Nobutarou/NiMH_Charger_DIY/v6.0/e2studio/NiMHCharger6.0/src/smc_gen/r_bsp/mcu/rl78_g24/register_access/llvm/iodefine.h

/*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
* Copyright (C) 2023 Renesas Electronics Corporation. All rights reserved.
***********************************************************************************************************************/
/***********************************************************************************************************************
* File Name    : iodefine.h
* Description  : 
***********************************************************************************************************************/
/***********************************************************************************************************************
* History : DD.MM.YYYY Version  Description
*         : 28.02.2023 1.60     First Release.
*         : 30.11.2023 1.62     Updated device file..
***********************************************************************************************************************/

#ifndef __INTRINSIC_FUNCTIONS
#define __INTRINSIC_FUNCTIONS

#define DI() __builtin_rl78_di()
#define EI() __builtin_rl78_ei()
#define HALT() __halt()
#define NOP() __nop()
#define STOP() __stop()

#endif

#ifndef __IOREG_BIT_STRUCTURES
#define __IOREG_BIT_STRUCTURES
typedef struct {
	unsigned char no0 :1;
	unsigned char no1 :1;
	unsigned char no2 :1;
	unsigned char no3 :1;
	unsigned char no4 :1;
	unsigned char no5 :1;
	unsigned char no6 :1;
	unsigned char no7 :1;
} __BITS8;

typedef struct {
	unsigned short no0 :1;
	unsigned short no1 :1;
	unsigned short no2 :1;
	unsigned short no3 :1;
	unsigned short no4 :1;
	unsigned short no5 :1;
	unsigned short no6 :1;
	unsigned short no7 :1;
	unsigned short no8 :1;
	unsigned short no9 :1;
	unsigned short no10 :1;
	unsigned short no11 :1;
	unsigned short no12 :1;
	unsigned short no13 :1;
	unsigned short no14 :1;
	unsigned short no15 :1;
} __BITS16;

#endif

#ifndef IODEFINE_H
#define IODEFINE_H

/*
 IO Registers
 */
union un_p0 {
	unsigned char p0;
	__BITS8 BIT;
};
union un_p1 {
	unsigned char p1;
	__BITS8 BIT;
};
union un_p2 {
	unsigned char p2;
	__BITS8 BIT;
};
union un_p3 {
	unsigned char p3;
	__BITS8 BIT;
};
union un_p4 {
	unsigned char p4;
	__BITS8 BIT;
};
union un_p5 {
	unsigned char p5;
	__BITS8 BIT;
};
union un_p6 {
	unsigned char p6;
	__BITS8 BIT;
};
union un_p7 {
	unsigned char p7;
	__BITS8 BIT;
};
union un_p12 {
	unsigned char p12;
	__BITS8 BIT;
};
union un_p13 {
	unsigned char p13;
	__BITS8 BIT;
};
union un_p14 {
	unsigned char p14;
	__BITS8 BIT;
};
union un_pm0 {
	unsigned char pm0;
	__BITS8 BIT;
};
union un_pm1 {
	unsigned char pm1;
	__BITS8 BIT;
};
union un_pm2 {
	unsigned char pm2;
	__BITS8 BIT;
};
union un_pm3 {
	unsigned char pm3;
	__BITS8 BIT;
};
union un_pm4 {
	unsigned char pm4;
	__BITS8 BIT;
};
union un_pm5 {
	unsigned char pm5;
	__BITS8 BIT;
};
union un_pm6 {
	unsigned char pm6;
	__BITS8 BIT;
};
union un_pm7 {
	unsigned char pm7;
	__BITS8 BIT;
};
union un_pm12 {
	unsigned char pm12;
	__BITS8 BIT;
};
union un_pm14 {
	unsigned char pm14;
	__BITS8 BIT;
};
union un_adm0 {
	unsigned char adm0;
	__BITS8 BIT;
};
union un_ads {
	unsigned char ads;
	__BITS8 BIT;
};
union un_adm1 {
	unsigned char adm1;
	__BITS8 BIT;
};
union un_krctl {
	unsigned char krctl;
	__BITS8 BIT;
};
union un_krm0 {
	unsigned char krm0;
	__BITS8 BIT;
};
union un_egp0 {
	unsigned char egp0;
	__BITS8 BIT;
};
union un_egn0 {
	unsigned char egn0;
	__BITS8 BIT;
};
union un_egp1 {
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
	__BITS8 BIT;
};
union un_pr10h {
	unsigned char pr10h;
	__BITS8 BIT;
};
union un_pr11 {
	unsigned short pr11;
	__BITS16 BIT;
};
union un_pr11l {
	unsigned char pr11l;
	__BITS8 BIT;
};
union un_pr11h {
	unsigned char pr11h;
	__BITS8 BIT;
};
union un_pmc {
	unsigned char pmc;
	__BITS8 BIT;
};

#define P0 (*(volatile union un_p0 *)0xFFF00).p0
#define P0_bit (*(volatile union un_p0 *)0xFFF00).BIT
#define P1 (*(volatile union un_p1 *)0xFFF01).p1
#define P1_bit (*(volatile union un_p1 *)0xFFF01).BIT
#define P2 (*(volatile union un_p2 *)0xFFF02).p2
#define P2_bit (*(volatile union un_p2 *)0xFFF02).BIT
#define P3 (*(volatile union un_p3 *)0xFFF03).p3
#define P3_bit (*(volatile union un_p3 *)0xFFF03).BIT
#define P4 (*(volatile union un_p4 *)0xFFF04).p4
#define P4_bit (*(volatile union un_p4 *)0xFFF04).BIT
#define P5 (*(volatile union un_p5 *)0xFFF05).p5
#define P5_bit (*(volatile union un_p5 *)0xFFF05).BIT
#define P6 (*(volatile union un_p6 *)0xFFF06).p6
#define P6_bit (*(volatile union un_p6 *)0xFFF06).BIT
#define P7 (*(volatile union un_p7 *)0xFFF07).p7
#define P7_bit (*(volatile union un_p7 *)0xFFF07).BIT
#define P12 (*(volatile union un_p12 *)0xFFF0C).p12
#define P12_bit (*(volatile union un_p12 *)0xFFF0C).BIT
#define P13 (*(volatile union un_p13 *)0xFFF0D).p13
#define P13_bit (*(volatile union un_p13 *)0xFFF0D).BIT
#define P14 (*(volatile union un_p14 *)0xFFF0E).p14
#define P14_bit (*(volatile union un_p14 *)0xFFF0E).BIT
#define SDR00 (*(volatile unsigned short *)0xFFF10)
#define TXD0 (*(volatile unsigned char *)0xFFF10)
#define SIO00 (*(volatile unsigned char *)0xFFF10)
#define SDR01 (*(volatile unsigned short *)0xFFF12)
#define RXD0 (*(volatile unsigned char *)0xFFF12)
#define SIO01 (*(volatile unsigned char *)0xFFF12)
#define TDR00 (*(volatile unsigned short *)0xFFF18)
#define TDR01 (*(volatile unsigned short *)0xFFF1A)
#define TDR01L (*(volatile unsigned char *)0xFFF1A)
#define TDR01H (*(volatile unsigned char *)0xFFF1B)
#define ADCR (*(volatile unsigned short *)0xFFF1E)
#define ADCRH (*(volatile unsigned char *)0xFFF1F)
#define PM0 (*(volatile union un_pm0 *)0xFFF20).pm0
#define PM0_bit (*(volatile union un_pm0 *)0xFFF20).BIT
#define PM1 (*(volatile union un_pm1 *)0xFFF21).pm1
#define PM1_bit (*(volatile union un_pm1 *)0xFFF21).BIT
#define PM2 (*(volatile union un_pm2 *)0xFFF22).pm2
#define PM2_bit (*(volatile union un_pm2 *)0xFFF22).BIT
#define PM3 (*(volatile union un_pm3 *)0xFFF23).pm3
#define PM3_bit (*(volatile union un_pm3 *)0xFFF23).BIT
#define PM4 (*(volatile union un_pm4 *)0xFFF24).pm4
#define PM4_bit (*(volatile union un_pm4 *)0xFFF24).BIT
#define PM5 (*(volatile union un_pm5 *)0xFFF25).pm5
#define PM5_bit (*(volatile union un_pm5 *)0xFFF25).BIT
#define PM6 (*(volatile union un_pm6 *)0xFFF26).pm6
#define PM6_bit (*(volatile union un_pm6 *)0xFFF26).BIT
#define PM7 (*(volatile union un_pm7 *)0xFFF27).pm7
#define PM7_bit (*(volatile union un_pm7 *)0xFFF27).BIT
#define PM12 (*(volatile union un_pm12 *)0xFFF2C).pm12
#define PM12_bit (*(volatile union un_pm12 *)0xFFF2C).BIT
#define PM14 (*(volatile union un_pm14 *)0xFFF2E).pm14
#define PM14_bit (*(volatile union un_pm14 *)0xFFF2E).BIT
#define ADM0 (*(volatile union un_adm0 *)0xFFF30).adm0
#define ADM0_bit (*(volatile union un_adm0 *)0xFFF30).BIT
#define ADS (*(volatile union un_ads *)0xFFF31).ads
#define ADS_bit (*(volatile union un_ads *)0xFFF31).BIT
#define ADM1 (*(volatile union un_adm1 *)0xFFF32).adm1
#define ADM1_bit (*(volatile union un_adm1 *)0xFFF32).BIT
#define KRCTL (*(volatile union un_krctl *)0xFFF34).krctl
#define KRCTL_bit (*(volatile union un_krctl *)0xFFF34).BIT
#define KRF (*(volatile unsigned char *)0xFFF35)
#define KRM0 (*(volatile union un_krm0 *)0xFFF37).krm0
#define KRM0_bit (*(volatile union un_krm0 *)0xFFF37).BIT
#define EGP0 (*(volatile union un_egp0 *)0xFFF38).egp0
#define EGP0_bit (*(volatile union un_egp0 *)0xFFF38).BIT
#define EGN0 (*(volatile union un_egn0 *)0xFFF39).egn0
#define EGN0_bit (*(volatile union un_egn0 *)0xFFF39).BIT
#define EGP1 (*(volatile union un_egp1 *)0xFFF3A).egp1
#define EGP1_bit (*(volatile union un_egp1 *)0xFFF3A).BIT
#define EGN1 (*(volatile union un_egn1 *)0xFFF3B).egn1
#define EGN1_bit (*(volatile union un_egn1 *)0xFFF3B).BIT
#define SDR02 (*(volatile unsigned short *)0xFFF44)
#define SIO10 (*(volatile unsigned char *)0xFFF44)
#define TXD1 (*(volatile unsigned char *)0xFFF44)
#define SDR03 (*(volatile unsigned short *)0xFFF46)
#define RXD1 (*(volatile unsigned char *)0xFFF46)
#define SIO11 (*(volatile unsigned char *)0xFFF46)
#define SDR10 (*(volatile unsigned short *)0xFFF48)
#define SIO20 (*(volatile unsigned char *)0xFFF48)
#define TXD2 (*(volatile unsigned char *)0xFFF48)
#define SDR11 (*(volatile unsigned short *)0xFFF4A)
#define SIO21 (*(volatile unsigned char *)0xFFF4A)
#define RXD2 (*(volatile unsigned char *)0xFFF4A)
#define IICA0 (*(volatile unsigned char *)0xFFF50)
#define IICS0 (*(volatile union un_iics0 *)0xFFF51).iics0
#define IICS0_bit (*(volatile union un_iics0 *)0xFFF51).BIT
#define IICF0 (*(volatile union un_iicf0 *)0xFFF52).iicf0
#define IICF0_bit (*(volatile union un_iicf0 *)0xFFF52).BIT
#define TRGGRC (*(volatile unsigned short *)0xFFF60)
#define TRGGRD (*(volatile unsigned short *)0xFFF62)
#define TDR02 (*(volatile unsigned short *)0xFFF64)
#define TDR03 (*(volatile unsigned short *)0xFFF66)
#define TDR03L (*(volatile unsigned char *)0xFFF66)
#define TDR03H (*(volatile unsigned char *)0xFFF67)
#define TRDGRC0 (*(volatile unsigned short *)0xFFF6C)
#define TRDGRD0 (*(volatile unsigned short *)0xFFF6E)
#define TRDGRC1 (*(volatile unsigned short *)0xFFF70)
#define TRDGRD1 (*(volatile unsigned short *)0xFFF72)
#define TRDCMPD0 (*(volatile unsigned short *)0xFFF74)
#define TRDCMPC1 (*(volatile unsigned short *)0xFFF76)
#define TRDCMPD1 (*(volatile unsigned short *)0xFFF78)
#define TRDADTB0 (*(volatile unsigned short *)0xFFF7A)
#define TRDCMPF1 (*(volatile unsigned short *)0xFFF7A)
#define TRDADTB1 (*(volatile unsigned short *)0xFFF7C)
#define TRDRDT (*(volatile unsigned short *)0xFFF7E)
#define TRDRDT0 (*(volatile unsigned char *)0xFFF7E)
#define TRDRDT1 (*(volatile unsigned char *)0xFFF7F)
#define CMC (*(volatile unsigned char *)0xFFFA0)
#define CSC (*(volatile union un_csc *)0xFFFA1).csc
#define CSC_bit (*(volatile union un_csc *)0xFFFA1).BIT
#define OSTC (*(volatile union un_ostc *)0xFFFA2).ostc
#define OSTC_bit (*(volatile union un_ostc *)0xFFFA2).BIT
#define OSTS (*(volatile unsigned char *)0xFFFA3)
#define CKC (*(volatile union un_ckc *)0xFFFA4).ckc
#define CKC_bit (*(volatile union un_ckc *)0xFFFA4).BIT
#define CKS0 (*(volatile union un_cks0 *)0xFFFA5).cks0
#define CKS0_bit (*(volatile union un_cks0 *)0xFFFA5).BIT
#define CKS1 (*(volatile union un_cks1 *)0xFFFA6).cks1
#define CKS1_bit (*(volatile union un_cks1 *)0xFFFA6).BIT
#define CKSEL (*(volatile union un_cksel *)0xFFFA7).cksel
#define CKSEL_bit (*(volatile union un_cksel *)0xFFFA7).BIT
#define RESF (*(volatile unsigned char *)0xFFFA8)
#define LVIM (*(volatile union un_lvim *)0xFFFA9).lvim
#define LVIM_bit (*(volatile union un_lvim *)0xFFFA9).BIT
#define LVIS (*(volatile union un_lvis *)0xFFFAA).lvis
#define LVIS_bit (*(volatile union un_lvis *)0xFFFAA).BIT
#define WDTE (*(volatile unsigned char *)0xFFFAB)
#define CRCIN (*(volatile unsigned char *)0xFFFAC)
#define IF2 (*(volatile union un_if2 *)0xFFFD0).if2
#define IF2_bit (*(volatile union un_if2 *)0xFFFD0).BIT
#define IF2L (*(volatile union un_if2l *)0xFFFD0).if2l
#define IF2L_bit (*(volatile union un_if2l *)0xFFFD0).BIT
#define IF2H (*(volatile union un_if2h *)0xFFFD1).if2h
#define IF2H_bit (*(volatile union un_if2h *)0xFFFD1).BIT
#define IF3 (*(volatile union un_if3 *)0xFFFD2).if3
#define IF3_bit (*(volatile union un_if3 *)0xFFFD2).BIT
#define IF3L (*(volatile union un_if3l *)0xFFFD2).if3l
#define IF3L_bit (*(volatile union un_if3l *)0xFFFD2).BIT
#define IF3H (*(volatile union un_if3h *)0xFFFD3).if3h
#define IF3H_bit (*(volatile union un_if3h *)0xFFFD3).BIT
#define MK2 (*(volatile union un_mk2 *)0xFFFD4).mk2
#define MK2_bit (*(volatile union un_mk2 *)0xFFFD4).BIT
#define MK2L (*(volatile union un_mk2l *)0xFFFD4).mk2l
#define MK2L_bit (*(volatile union un_mk2l *)0xFFFD4).BIT
#define MK2H (*(volatile union un_mk2h *)0xFFFD5).mk2h
#define MK2H_bit (*(volatile union un_mk2h *)0xFFFD5).BIT
#define MK3 (*(volatile union un_mk3 *)0xFFFD6).mk3
#define MK3_bit (*(volatile union un_mk3 *)0xFFFD6).BIT
#define MK3L (*(volatile union un_mk3l *)0xFFFD6).mk3l
#define MK3L_bit (*(volatile union un_mk3l *)0xFFFD6).BIT
#define MK3H (*(volatile union un_mk3h *)0xFFFD7).mk3h
#define MK3H_bit (*(volatile union un_mk3h *)0xFFFD7).BIT
#define PR02 (*(volatile union un_pr02 *)0xFFFD8).pr02
#define PR02_bit (*(volatile union un_pr02 *)0xFFFD8).BIT
#define PR02L (*(volatile union un_pr02l *)0xFFFD8).pr02l
#define PR02L_bit (*(volatile union un_pr02l *)0xFFFD8).BIT
#define PR02H (*(volatile union un_pr02h *)0xFFFD9).pr02h
#define PR02H_bit (*(volatile union un_pr02h *)0xFFFD9).BIT
#define PR03 (*(volatile union un_pr03 *)0xFFFDA).pr03
#define PR03_bit (*(volatile union un_pr03 *)0xFFFDA).BIT
#define PR03L (*(volatile union un_pr03l *)0xFFFDA).pr03l
#define PR03L_bit (*(volatile union un_pr03l *)0xFFFDA).BIT
#define PR03H (*(volatile union un_pr03h *)0xFFFDB).pr03h
#define PR03H_bit (*(volatile union un_pr03h *)0xFFFDB).BIT
#define PR12 (*(volatile union un_pr12 *)0xFFFDC).pr12
#define PR12_bit (*(volatile union un_pr12 *)0xFFFDC).BIT
#define PR12L (*(volatile union un_pr12l *)0xFFFDC).pr12l
#define PR12L_bit (*(volatile union un_pr12l *)0xFFFDC).BIT
#define PR12H (*(volatile union un_pr12h *)0xFFFDD).pr12h
#define PR12H_bit (*(volatile union un_pr12h *)0xFFFDD).BIT
#define PR13 (*(volatile union un_pr13 *)0xFFFDE).pr13
#define PR13_bit (*(volatile union un_pr13 *)0xFFFDE).BIT
#define PR13L (*(volatile union un_pr13l *)0xFFFDE).pr13l
#define PR13L_bit (*(volatile union un_pr13l *)0xFFFDE).BIT
#define PR13H (*(volatile union un_pr13h *)0xFFFDF).pr13h
#define PR13H_bit (*(volatile union un_pr13h *)0xFFFDF).BIT
#define IF0 (*(volatile union un_if0 *)0xFFFE0).if0
#define IF0_bit (*(volatile union un_if0 *)0xFFFE0).BIT
#define IF0L (*(volatile union un_if0l *)0xFFFE0).if0l
#define IF0L_bit (*(volatile union un_if0l *)0xFFFE0).BIT
#define IF0H (*(volatile union un_if0h *)0xFFFE1).if0h
#define IF0H_bit (*(volatile union un_if0h *)0xFFFE1).BIT
#define IF1 (*(volatile union un_if1 *)0xFFFE2).if1
#define IF1_bit (*(volatile union un_if1 *)0xFFFE2).BIT
#define IF1L (*(volatile union un_if1l *)0xFFFE2).if1l
#define IF1L_bit (*(volatile union un_if1l *)0xFFFE2).BIT
#define IF1H (*(volatile union un_if1h *)0xFFFE3).if1h
#define IF1H_bit (*(volatile union un_if1h *)0xFFFE3).BIT
#define MK0 (*(volatile union un_mk0 *)0xFFFE4).mk0
#define MK0_bit (*(volatile union un_mk0 *)0xFFFE4).BIT
#define MK0L (*(volatile union un_mk0l *)0xFFFE4).mk0l
#define MK0L_bit (*(volatile union un_mk0l *)0xFFFE4).BIT
#define MK0H (*(volatile union un_mk0h *)0xFFFE5).mk0h
#define MK0H_bit (*(volatile union un_mk0h *)0xFFFE5).BIT
#define MK1 (*(volatile union un_mk1 *)0xFFFE6).mk1
#define MK1_bit (*(volatile union un_mk1 *)0xFFFE6).BIT
#define MK1L (*(volatile union un_mk1l *)0xFFFE6).mk1l
#define MK1L_bit (*(volatile union un_mk1l *)0xFFFE6).BIT
#define MK1H (*(volatile union un_mk1h *)0xFFFE7).mk1h
#define MK1H_bit (*(volatile union un_mk1h *)0xFFFE7).BIT
#define PR00 (*(volatile union un_pr00 *)0xFFFE8).pr00
#define PR00_bit (*(volatile union un_pr00 *)0xFFFE8).BIT
#define PR00L (*(volatile union un_pr00l *)0xFFFE8).pr00l
#define PR00L_bit (*(volatile union un_pr00l *)0xFFFE8).BIT
#define PR00H (*(volatile union un_pr00h *)0xFFFE9).pr00h
#define PR00H_bit (*(volatile union un_pr00h *)0xFFFE9).BIT
#define PR01 (*(volatile union un_pr01 *)0xFFFEA).pr01
#define PR01_bit (*(volatile union un_pr01 *)0xFFFEA).BIT
#define PR01L (*(volatile union un_pr01l *)0xFFFEA).pr01l
#define PR01L_bit (*(volatile union un_pr01l *)0xFFFEA).BIT
#define PR01H (*(volatile union un_pr01h *)0xFFFEB).pr01h
#define PR01H_bit (*(volatile union un_pr01h *)0xFFFEB).BIT
#define PR10 (*(volatile union un_pr10 *)0xFFFEC).pr10
#define PR10_bit (*(volatile union un_pr10 *)0xFFFEC).BIT
#define PR10L (*(volatile union un_pr10l *)0xFFFEC).pr10l
#define PR10L_bit (*(volatile union un_pr10l *)0xFFFEC).BIT
#define PR10H (*(volatile union un_pr10h *)0xFFFED).pr10h
#define PR10H_bit (*(volatile union un_pr10h *)0xFFFED).BIT
#define PR11 (*(volatile union un_pr11 *)0xFFFEE).pr11
#define PR11_bit (*(volatile union un_pr11 *)0xFFFEE).BIT
#define PR11L (*(volatile union un_pr11l *)0xFFFEE).pr11l
#define PR11L_bit (*(volatile union un_pr11l *)0xFFFEE).BIT
#define PR11H (*(volatile union un_pr11h *)0xFFFEF).pr11h
#define PR11H_bit (*(volatile union un_pr11h *)0xFFFEF).BIT
#define MACRL (*(volatile unsigned short *)0xFFFF0)
#define MACRH (*(volatile unsigned short *)0xFFFF2)
#define PMC (*(volatile union un_pmc *)0xFFFFE).pmc
#define PMC_bit (*(volatile union un_pmc *)0xFFFFE).BIT

/*
 Sfr bits
 */
#define ADCE ADM0_bit.no0
#define ADCS ADM0_bit.no7
#define KREG KRCTL_bit.no0
#define KRMD KRCTL_bit.no7
#define SPD0 IICS0_bit.no0
#define STD0 IICS0_bit.no1
#define ACKD0 IICS0_bit.no2
#define TRC0 IICS0_bit.no3
#define COI0 IICS0_bit.no4
#define EXC0 IICS0_bit.no5
#define ALD0 IICS0_bit.no6
#define MSTS0 IICS0_bit.no7
#define IICRSV0 IICF0_bit.no0
#define STCEN0 IICF0_bit.no1
#define IICBSY0 IICF0_bit.no6
#define STCF0 IICF0_bit.no7
#define HIOSTOP CSC_bit.no0
#define MIOEN CSC_bit.no1
#define XTSTOP CSC_bit.no6
#define MSTOP CSC_bit.no7
#define MCM1 CKC_bit.no0
#define MCS1 CKC_bit.no1
#define MCM0 CKC_bit.no4
#define MCS CKC_bit.no5
#define CSS CKC_bit.no6
#define CLS CKC_bit.no7
#define PCLOE0 CKS0_bit.no7
#define PCLOE1 CKS1_bit.no7
#define SELLOSC CKSEL_bit.no0
#define LVD0F LVIM_bit.no0
#define LVD1F LVIM_bit.no1
#define DLVD0F LVIM_bit.no2
#define DLVD1F LVIM_bit.no3
#define LVISEN LVIM_bit.no7
#define LVD1SEL LVIS_bit.no6
#define LVD1EN LVIS_bit.no7
#define BPDIF IF2L_bit.no0
#define CLDIF IF2L_bit.no0
#define TRXIF IF2L_bit.no0
#define EDIF IF2L_bit.no0
#define PIF20 IF2L_bit.no1
#define PIF21 IF2L_bit.no2
#define PIF6 IF2L_bit.no3
#define TMKBSTRIF10 IF2L_bit.no3
#define PIF7 IF2L_bit.no4
#define TMKBSTPIF10 IF2L_bit.no4
#define TMKBSTRIF11 IF2L_bit.no5
#define PIF8 IF2L_bit.no5
#define PIF9 IF2L_bit.no6
#define TMKBSTPIF11 IF2L_bit.no6
#define FLIF IF2L_bit.no7
#define PIF10 IF2H_bit.no0
#define CMPIF0 IF2H_bit.no0
#define PIF11 IF2H_bit.no1
#define CMPIF1 IF2H_bit.no1
#define FAATRAPIF IF2H_bit.no2
#define CMPIF2 IF2H_bit.no3
#define CMPIF3 IF2H_bit.no4
#define TMKBIF0 IF2H_bit.no5
#define TMKBIF1 IF2H_bit.no6
#define TMKBIF2 IF2H_bit.no7
#define SDDIF IF3L_bit.no0
#define GCRIF IF3L_bit.no0
#define PMCIF IF3L_bit.no1
#define FEDIF IF3L_bit.no1
#define TMKBSTRIF00 IF3L_bit.no2
#define TMKBSTPIF00 IF3L_bit.no3
#define TMKBSTRIF01 IF3L_bit.no4
#define TMKBSTPIF01 IF3L_bit.no5
#define TMKBSTRIF20 IF3L_bit.no6
#define TMKBSTPIF20 IF3L_bit.no7
#define TMKBSTRIF21 IF3H_bit.no0
#define TMKBSTPIF21 IF3H_bit.no1
#define TIMECIF1 IF3H_bit.no2
#define TIMECIF2 IF3H_bit.no3
#define ADIF3 IF3H_bit.no4
#define EDMK MK2L_bit.no0
#define TRXMK MK2L_bit.no0
#define BPDMK MK2L_bit.no0
#define CLDMK MK2L_bit.no0
#define PMK20 MK2L_bit.no1
#define PMK21 MK2L_bit.no2
#define PMK6 MK2L_bit.no3
#define TMKBSTRMK10 MK2L_bit.no3
#define PMK7 MK2L_bit.no4
#define TMKBSTPMK10 MK2L_bit.no4
#define PMK8 MK2L_bit.no5
#define TMKBSTRMK11 MK2L_bit.no5
#define TMKBSTPMK11 MK2L_bit.no6
#define PMK9 MK2L_bit.no6
#define FLMK MK2L_bit.no7
#define PMK10 MK2H_bit.no0
#define CMPMK0 MK2H_bit.no0
#define PMK11 MK2H_bit.no1
#define CMPMK1 MK2H_bit.no1
#define FAATRAPMK MK2H_bit.no2
#define CMPMK2 MK2H_bit.no3
#define CMPMK3 MK2H_bit.no4
#define TMKBMK0 MK2H_bit.no5
#define TMKBMK1 MK2H_bit.no6
#define TMKBMK2 MK2H_bit.no7
#define GCRMK MK3L_bit.no0
#define SDDMK MK3L_bit.no0
#define PMCMK MK3L_bit.no1
#define FEDMK MK3L_bit.no1
#define TMKBSTRMK00 MK3L_bit.no2
#define TMKBSTPMK00 MK3L_bit.no3
#define TMKBSTRMK01 MK3L_bit.no4
#define TMKBSTPMK01 MK3L_bit.no5
#define TMKBSTRMK20 MK3L_bit.no6
#define TMKBSTPMK20 MK3L_bit.no7
#define TMKBSTRMK21 MK3H_bit.no0
#define TMKBSTPMK21 MK3H_bit.no1
#define TIMECMK1 MK3H_bit.no2
#define TIMECMK2 MK3H_bit.no3
#define ADMK3 MK3H_bit.no4
#define EDPR0 PR02L_bit.no0
#define TRXPR0 PR02L_bit.no0
#define BPDPR0 PR02L_bit.no0
#define CLDPR0 PR02L_bit.no0
#define PPR020 PR02L_bit.no1
#define PPR021 PR02L_bit.no2
#define TMKBSTRPR010 PR02L_bit.no3
#define PPR06 PR02L_bit.no3
#define TMKBSTPPR010 PR02L_bit.no4
#define PPR07 PR02L_bit.no4
#define TMKBSTRPR011 PR02L_bit.no5
#define PPR08 PR02L_bit.no5
#define PPR09 PR02L_bit.no6
#define TMKBSTPPR011 PR02L_bit.no6
#define FLPR0 PR02L_bit.no7
#define PPR010 PR02H_bit.no0
#define CMPPR00 PR02H_bit.no0
#define PPR011 PR02H_bit.no1
#define CMPPR01 PR02H_bit.no1
#define FAATRAPPR0 PR02H_bit.no2
#define CMPPR02 PR02H_bit.no3
#define CMPPR03 PR02H_bit.no4
#define TMKBPR00 PR02H_bit.no5
#define TMKBPR01 PR02H_bit.no6
#define TMKBPR02 PR02H_bit.no7
#define SDDPR0 PR03L_bit.no0
#define GCRPR0 PR03L_bit.no0
#define PMCPR0 PR03L_bit.no1
#define FEDPR0 PR03L_bit.no1
#define TMKBSTRPR000 PR03L_bit.no2
#define TMKBSTPPR000 PR03L_bit.no3
#define TMKBSTRPR001 PR03L_bit.no4
#define TMKBSTPPR001 PR03L_bit.no5
#define TMKBSTRPR020 PR03L_bit.no6
#define TMKBSTPPR020 PR03L_bit.no7
#define TMKBSTRPR021 PR03H_bit.no0
#define TMKBSTPPR021 PR03H_bit.no1
#define TIMECPR01 PR03H_bit.no2
#define TIMECPR02 PR03H_bit.no3
#define ADPR03 PR03H_bit.no4
#define EDPR1 PR12L_bit.no0
#define BPDPR1 PR12L_bit.no0
#define TRXPR1 PR12L_bit.no0
#define CLDPR1 PR12L_bit.no0
#define PPR120 PR12L_bit.no1
#define PPR121 PR12L_bit.no2
#define PPR16 PR12L_bit.no3
#define TMKBSTRPR110 PR12L_bit.no3
#define PPR17 PR12L_bit.no4
#define TMKBSTPPR110 PR12L_bit.no4
#define PPR18 PR12L_bit.no5
#define TMKBSTRPR111 PR12L_bit.no5
#define PPR19 PR12L_bit.no6
#define TMKBSTPPR111 PR12L_bit.no6
#define FLPR1 PR12L_bit.no7
#define PPR110 PR12H_bit.no0
#define CMPPR10 PR12H_bit.no0
#define PPR111 PR12H_bit.no1
#define CMPPR11 PR12H_bit.no1
#define FAATRAPPR1 PR12H_bit.no2
#define CMPPR12 PR12H_bit.no3
#define CMPPR13 PR12H_bit.no4
#define TMKBPR10 PR12H_bit.no5
#define TMKBPR11 PR12H_bit.no6
#define TMKBPR12 PR12H_bit.no7
#define SDDPR1 PR13L_bit.no0
#define GCRPR1 PR13L_bit.no0
#define PMCPR1 PR13L_bit.no1
#define FEDPR1 PR13L_bit.no1
#define TMKBSTRPR100 PR13L_bit.no2
#define TMKBSTPPR100 PR13L_bit.no3
#define TMKBSTRPR101 PR13L_bit.no4
#define TMKBSTPPR101 PR13L_bit.no5
#define TMKBSTRPR120 PR13L_bit.no6
#define TMKBSTPPR120 PR13L_bit.no7
#define TMKBSTRPR121 PR13H_bit.no0
#define TMKBSTPPR121 PR13H_bit.no1
#define TIMECPR11 PR13H_bit.no2
#define TIMECPR12 PR13H_bit.no3
#define ADPR13 PR13H_bit.no4
#define WDTIIF IF0L_bit.no0
#define LVIIF IF0L_bit.no1
#define PIF0 IF0L_bit.no2
#define PIF1 IF0L_bit.no3
#define ADIF1 IF0L_bit.no3
#define PIF2 IF0L_bit.no4
#define ADIF2 IF0L_bit.no4
#define PIF3 IF0L_bit.no5
#define PIF4 IF0L_bit.no6
#define PIF5 IF0L_bit.no7
#define STIF2 IF0H_bit.no0
#define CSIIF20 IF0H_bit.no0
#define IICIF20 IF0H_bit.no0
#define SRIF2 IF0H_bit.no1
#define IICIF21 IF0H_bit.no1
#define CSIIF21 IF0H_bit.no1
#define SREIF2 IF0H_bit.no2
#define FAAEIF IF0H_bit.no3
#define TIMECIF0 IF0H_bit.no4
#define STIF0 IF0H_bit.no5
#define IICIF00 IF0H_bit.no5
#define CSIIF00 IF0H_bit.no5
#define TMIF00 IF0H_bit.no6
#define SREIF0 IF0H_bit.no7
#define TMIF01H IF0H_bit.no7
#define STIF1 IF1L_bit.no0
#define IICIF10 IF1L_bit.no0
#define CSIIF10 IF1L_bit.no0
#define SRIF1 IF1L_bit.no1
#define CSIIF11 IF1L_bit.no1
#define IICIF11 IF1L_bit.no1
#define SREIF1 IF1L_bit.no2
#define TMIF03H IF1L_bit.no2
#define IICAIF0 IF1L_bit.no3
#define SRIF0 IF1L_bit.no4
#define CSIIF01 IF1L_bit.no4
#define IICIF01 IF1L_bit.no4
#define TMIF01 IF1L_bit.no5
#define TMIF02 IF1L_bit.no6
#define TMIF03 IF1L_bit.no7
#define ADIF0 IF1H_bit.no0
#define RTCIF IF1H_bit.no1
#define ITLIF IF1H_bit.no2
#define KRIF IF1H_bit.no3
#define TDIF IF1H_bit.no4
#define TRJIF0 IF1H_bit.no4
#define TRDIF0 IF1H_bit.no5
#define TRDIF1 IF1H_bit.no6
#define TRGIF IF1H_bit.no7
#define RDIF IF1H_bit.no7
#define WDTIMK MK0L_bit.no0
#define LVIMK MK0L_bit.no1
#define PMK0 MK0L_bit.no2
#define PMK1 MK0L_bit.no3
#define ADMK1 MK0L_bit.no3
#define ADMK2 MK0L_bit.no4
#define PMK2 MK0L_bit.no4
#define PMK3 MK0L_bit.no5
#define PMK4 MK0L_bit.no6
#define PMK5 MK0L_bit.no7
#define IICMK20 MK0H_bit.no0
#define CSIMK20 MK0H_bit.no0
#define STMK2 MK0H_bit.no0
#define SRMK2 MK0H_bit.no1
#define CSIMK21 MK0H_bit.no1
#define IICMK21 MK0H_bit.no1
#define SREMK2 MK0H_bit.no2
#define FAAEMK MK0H_bit.no3
#define TIMECMK0 MK0H_bit.no4
#define IICMK00 MK0H_bit.no5
#define CSIMK00 MK0H_bit.no5
#define STMK0 MK0H_bit.no5
#define TMMK00 MK0H_bit.no6
#define SREMK0 MK0H_bit.no7
#define TMMK01H MK0H_bit.no7
#define STMK1 MK1L_bit.no0
#define CSIMK10 MK1L_bit.no0
#define IICMK10 MK1L_bit.no0
#define SRMK1 MK1L_bit.no1
#define IICMK11 MK1L_bit.no1
#define CSIMK11 MK1L_bit.no1
#define SREMK1 MK1L_bit.no2
#define TMMK03H MK1L_bit.no2
#define IICAMK0 MK1L_bit.no3
#define SRMK0 MK1L_bit.no4
#define IICMK01 MK1L_bit.no4
#define CSIMK01 MK1L_bit.no4
#define TMMK01 MK1L_bit.no5
#define TMMK02 MK1L_bit.no6
#define TMMK03 MK1L_bit.no7
#define ADMK0 MK1H_bit.no0
#define RTCMK MK1H_bit.no1
#define ITLMK MK1H_bit.no2
#define KRMK MK1H_bit.no3
#define TDMK MK1H_bit.no4
#define TRJMK0 MK1H_bit.no4
#define TRDMK0 MK1H_bit.no5
#define TRDMK1 MK1H_bit.no6
#define TRGMK MK1H_bit.no7
#define RDMK MK1H_bit.no7
#define WDTIPR0 PR00L_bit.no0
#define LVIPR0 PR00L_bit.no1
#define PPR00 PR00L_bit.no2
#define PPR01 PR00L_bit.no3
#define ADPR01 PR00L_bit.no3
#define PPR02 PR00L_bit.no4
#define ADPR02 PR00L_bit.no4
#define PPR03 PR00L_bit.no5
#define PPR04 PR00L_bit.no6
#define PPR05 PR00L_bit.no7
#define CSIPR020 PR00H_bit.no0
#define IICPR020 PR00H_bit.no0
#define STPR02 PR00H_bit.no0
#define SRPR02 PR00H_bit.no1
#define CSIPR021 PR00H_bit.no1
#define IICPR021 PR00H_bit.no1
#define SREPR02 PR00H_bit.no2
#define FAAEPR0 PR00H_bit.no3
#define TIMECPR00 PR00H_bit.no4
#define CSIPR000 PR00H_bit.no5
#define IICPR000 PR00H_bit.no5
#define STPR00 PR00H_bit.no5
#define TMPR000 PR00H_bit.no6
#define SREPR00 PR00H_bit.no7
#define TMPR001H PR00H_bit.no7
#define CSIPR010 PR01L_bit.no0
#define IICPR010 PR01L_bit.no0
#define STPR01 PR01L_bit.no0
#define SRPR01 PR01L_bit.no1
#define CSIPR011 PR01L_bit.no1
#define IICPR011 PR01L_bit.no1
#define SREPR01 PR01L_bit.no2
#define TMPR003H PR01L_bit.no2
#define IICAPR00 PR01L_bit.no3
#define SRPR00 PR01L_bit.no4
#define CSIPR001 PR01L_bit.no4
#define IICPR001 PR01L_bit.no4
#define TMPR001 PR01L_bit.no5
#define TMPR002 PR01L_bit.no6
#define TMPR003 PR01L_bit.no7
#define ADPR00 PR01H_bit.no0
#define RTCPR0 PR01H_bit.no1
#define ITLPR0 PR01H_bit.no2
#define KRPR0 PR01H_bit.no3
#define TRJPR00 PR01H_bit.no4
#define TDPR0 PR01H_bit.no4
#define TRDPR00 PR01H_bit.no5
#define TRDPR01 PR01H_bit.no6
#define TRGPR0 PR01H_bit.no7
#define RDPR0 PR01H_bit.no7
#define WDTIPR1 PR10L_bit.no0
#define LVIPR1 PR10L_bit.no1
#define PPR10 PR10L_bit.no2
#define PPR11 PR10L_bit.no3
#define ADPR11 PR10L_bit.no3
#define PPR12 PR10L_bit.no4
#define ADPR12 PR10L_bit.no4
#define PPR13 PR10L_bit.no5
#define PPR14 PR10L_bit.no6
#define PPR15 PR10L_bit.no7
#define IICPR120 PR10H_bit.no0
#define CSIPR120 PR10H_bit.no0
#define STPR12 PR10H_bit.no0
#define IICPR121 PR10H_bit.no1
#define CSIPR121 PR10H_bit.no1
#define SRPR12 PR10H_bit.no1
#define SREPR12 PR10H_bit.no2
#define FAAEPR1 PR10H_bit.no3
#define TIMECPR10 PR10H_bit.no4
#define CSIPR100 PR10H_bit.no5
#define IICPR100 PR10H_bit.no5
#define STPR10 PR10H_bit.no5
#define TMPR100 PR10H_bit.no6
#define TMPR101H PR10H_bit.no7
#define SREPR10 PR10H_bit.no7
#define IICPR110 PR11L_bit.no0
#define STPR11 PR11L_bit.no0
#define CSIPR110 PR11L_bit.no0
#define IICPR111 PR11L_bit.no1
#define CSIPR111 PR11L_bit.no1
#define SRPR11 PR11L_bit.no1
#define SREPR11 PR11L_bit.no2
#define TMPR103H PR11L_bit.no2
#define IICAPR10 PR11L_bit.no3
#define IICPR101 PR11L_bit.no4
#define SRPR10 PR11L_bit.no4
#define CSIPR101 PR11L_bit.no4
#define TMPR101 PR11L_bit.no5
#define TMPR102 PR11L_bit.no6
#define TMPR103 PR11L_bit.no7
#define ADPR10 PR11H_bit.no0
#define RTCPR1 PR11H_bit.no1
#define ITLPR1 PR11H_bit.no2
#define KRPR1 PR11H_bit.no3
#define TDPR1 PR11H_bit.no4
#define TRJPR10 PR11H_bit.no4
#define TRDPR10 PR11H_bit.no5
#define TRDPR11 PR11H_bit.no6
#define TRGPR1 PR11H_bit.no7
#define RDPR1 PR11H_bit.no7
#define MAA PMC_bit.no0

/*
 Interrupt vector addresses
 */
#define RST_vect 0x0
#define INTDBG_vect 0x2
#define INTWDTI_vect 0x4
#define INTLVI_vect 0x6
#define INTP0_vect 0x8
#define INTAD1_vect 0xA
#define INTP1_vect 0xA
#define INTAD2_vect 0xC
#define INTP2_vect 0xC
#define INTP3_vect 0xE
#define INTP4_vect 0x10
#define INTP5_vect 0x12
#define INTCSI20_vect 0x14
#define INTIIC20_vect 0x14
#define INTST2_vect 0x14
#define INTCSI21_vect 0x16
#define INTIIC21_vect 0x16
#define INTSR2_vect 0x16
#define INTSRE2_vect 0x18
#define INTFAAE_vect 0x1A
#define INTTIMEC0_vect 0x1C
#define INTCSI00_vect 0x1E
#define INTIIC00_vect 0x1E
#define INTST0_vect 0x1E
#define INTTM00_vect 0x20
#define INTSRE0_vect 0x22
#define INTTM01H_vect 0x22
#define INTCSI10_vect 0x24
#define INTIIC10_vect 0x24
#define INTST1_vect 0x24
#define INTCSI11_vect 0x26
#define INTIIC11_vect 0x26
#define INTSR1_vect 0x26
#define INTSRE1_vect 0x28
#define INTTM03H_vect 0x28
#define INTIICA0_vect 0x2A
#define INTCSI01_vect 0x2C
#define INTIIC01_vect 0x2C
#define INTSR0_vect 0x2C
#define INTTM01_vect 0x2E
#define INTTM02_vect 0x30
#define INTTM03_vect 0x32
#define INTAD0_vect 0x34
#define INTRTC_vect 0x36
#define INTITL_vect 0x38
#define INTKR_vect 0x3A
#define INTTD_vect 0x3C
#define INTTRJ0_vect 0x3C
#define INTTRD0_vect 0x3E
#define INTTRD1_vect 0x40
#define INTRD_vect 0x42
#define INTTRG_vect 0x42
#define INTBPD_vect 0x44
#define INTCLD_vect 0x44
#define INTED_vect 0x44
#define INTTRX_vect 0x44
#define INTP20_vect 0x46
#define INTP21_vect 0x48
#define INTP6_vect 0x4A
#define INTTMKBSTR10_vect 0x4A
#define INTP7_vect 0x4C
#define INTTMKBSTP10_vect 0x4C
#define INTP8_vect 0x4E
#define INTTMKBSTR11_vect 0x4E
#define INTP9_vect 0x50
#define INTTMKBSTP11_vect 0x50
#define INTFL_vect 0x52
#define INTCMP0_vect 0x54
#define INTP10_vect 0x54
#define INTCMP1_vect 0x56
#define INTP11_vect 0x56
#define INTFAATRAP_vect 0x58
#define INTCMP2_vect 0x5A
#define INTCMP3_vect 0x5C
#define INTTMKB0_vect 0x5E
#define INTTMKB1_vect 0x60
#define INTTMKB2_vect 0x62
#define INTGCR_vect 0x64
#define INTSDD_vect 0x64
#define INTFED_vect 0x66
#define INTPMC_vect 0x66
#define INTTMKBSTR00_vect 0x68
#define INTTMKBSTP00_vect 0x6A
#define INTTMKBSTR01_vect 0x6C
#define INTTMKBSTP01_vect 0x6E
#define INTTMKBSTR20_vect 0x70
#define INTTMKBSTP20_vect 0x72
#define INTTMKBSTR21_vect 0x74
#define INTTMKBSTP21_vect 0x76
#define INTTIMEC1_vect 0x78
#define INTTIMEC2_vect 0x7A
#define INTAD3_vect 0x7C
#define BRK_I_vect 0x7E
#endif
