Nobutarou/NiMH_Charger_DIY/v6.0/e2studio/NiMHCharger6.0/src/smc_gen/general/r_cg_inthandler.c

/*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
* Copyright (C) 2021, 2025 Renesas Electronics Corporation. All rights reserved.
***********************************************************************************************************************/

/***********************************************************************************************************************
* File Name        : r_cg_inthandler.c
* Version          : 1.0.50
* Device(s)        : R7F101G6ExSP
* Description      : None
***********************************************************************************************************************/

/***********************************************************************************************************************
Includes
***********************************************************************************************************************/
#include "r_cg_interrupt_handlers.h"

/*
 * INT_WDTI (0x4)
 */
void INT_WDTI (void)
{
    /* Start user code for INT_WDTI. Do not edit comment generated here */
    /* End user code. Do not edit comment generated here */
}

/*
 * INT_LVI (0x6)
 */
void INT_LVI (void)
{
    /* Start user code for INT_LVI. Do not edit comment generated here */
    /* End user code. Do not edit comment generated here */
}

/*
 * INT_P0 (0x8)
 */
void INT_P0 (void)
{
    /* Start user code for INT_P0. Do not edit comment generated here */
    /* End user code. Do not edit comment generated here */
}

/*
 * INT_P1/INT_AD1 (0xA)
 */
void INT_P1 (void)
{
    /* Start user code for INT_P1. Do not edit comment generated here */
    /* End user code. Do not edit comment generated here */
}
//void INT_AD1 (void) { }

/*
 * INT_P2/INT_AD2 (0xC)
 */
void INT_P2 (void)
{
    /* Start user code for INT_P2. Do not edit comment generated here */
    /* End user code. Do not edit comment generated here */
}
//void INT_AD2 (void) { }

/*
 * INT_P3 (0xE)
 */
void INT_P3 (void)
{
    /* Start user code for INT_P3. Do not edit comment generated here */
    /* End user code. Do not edit comment generated here */
}

/*
 * INT_P4 (0x10)
 */
void INT_P4 (void)
{
    /* Start user code for INT_P4. Do not edit comment generated here */
    /* End user code. Do not edit comment generated here */
}

/*
 * INT_P5 (0x12)
 */
void INT_P5 (void)
{
    /* Start user code for INT_P5. Do not edit comment generated here */
    /* End user code. Do not edit comment generated here */
}

/*
 * INT_CSI20/INT_IIC20/INT_ST2 (0x14)
 */
void INT_ST2 (void)
{
    /* Start user code for INT_ST2. Do not edit comment generated here */
    /* End user code. Do not edit comment generated here */
}
//void INT_CSI20 (void) { }
//void INT_IIC20 (void) { }

/*
 * INT_CSI21/INT_IIC21/INT_SR2 (0x16)
 */
void INT_SR2 (void)
{
    /* Start user code for INT_SR2. Do not edit comment generated here */
    /* End user code. Do not edit comment generated here */
}
//void INT_CSI21 (void) { }
//void INT_IIC21 (void) { }

/*
 * INT_SRE2 (0x18)
 */
void INT_SRE2 (void)
{
    /* Start user code for INT_SRE2. Do not edit comment generated here */
    /* End user code. Do not edit comment generated here */
}

/*
 * INT_FAAE (0x1A)
 */
void INT_FAAE (void)
{
    /* Start user code for INT_FAAE. Do not edit comment generated here */
    /* End user code. Do not edit comment generated here */
}

/*
 * INT_TIMEC0 (0x1C)
 */
void INT_TIMEC0 (void)
{
    /* Start user code for INT_TIMEC0. Do not edit comment generated here */
    /* End user code. Do not edit comment generated here */
}

/*
 * INT_CSI00/INT_IIC00/INT_ST0 (0x1E)
 */
void INT_ST0 (void)
{
    /* Start user code for INT_ST0. Do not edit comment generated here */
    /* End user code. Do not edit comment generated here */
}
//void INT_CSI00 (void) { }
//void INT_IIC00 (void) { }

/*
 * INT_TM00 (0x20)
 */
void INT_TM00 (void)
{
    /* Start user code for INT_TM00. Do not edit comment generated here */
    /* End user code. Do not edit comment generated here */
}

/*
 * INT_SRE0/INT_TM01H (0x22)
 */
void INT_TM01H (void)
{
    /* Start user code for INT_TM01H. Do not edit comment generated here */
    /* End user code. Do not edit comment generated here */
}
//void INT_SRE0 (void) { }

/*
 * INT_CSI10/INT_IIC10/INT_ST1 (0x24)
 */
void INT_ST1 (void)
{
    /* Start user code for INT_ST1. Do not edit comment generated here */
    /* End user code. Do not edit comment generated here */
}
//void INT_CSI10 (void) { }
//void INT_IIC10 (void) { }

/*
 * INT_CSI11/INT_IIC11/INT_SR1 (0x26)
 */
void INT_SR1 (void)
{
    /* Start user code for INT_SR1. Do not edit comment generated here */
    /* End user code. Do not edit comment generated here */
}
//void INT_CSI11 (void) { }
//void INT_IIC11 (void) { }

/*
 * INT_SRE1/INT_TM03H (0x28)
 */
void INT_TM03H (void)
{
    /* Start user code for INT_TM03H. Do not edit comment generated here */
    /* End user code. Do not edit comment generated here */
}
//void INT_SRE1 (void) { }

/*
 * INT_IICA0 (0x2A)
 */
void INT_IICA0 (void) 
{
    /* Start user code for INT_IICA0. Do not edit comment generated here */
    /* End user code. Do not edit comment generated here */
}

/*
 * INT_CSI01/INT_IIC01/INT_SR0 (0x2C)
 */
void INT_SR0 (void)
{
    /* Start user code for INT_SR0. Do not edit comment generated here */
    /* End user code. Do not edit comment generated here */
}
//void INT_CSI01 (void) { }
//void INT_IIC01 (void) { }

/*
 * INT_TM01 (0x2E)
 */
void INT_TM01 (void)
{
    /* Start user code for INT_TM01. Do not edit comment generated here */
    /* End user code. Do not edit comment generated here */
}

/*
 * INT_TM02 (0x30)
 */
void INT_TM02 (void)
{
    /* Start user code for INT_TM02. Do not edit comment generated here */
    /* End user code. Do not edit comment generated here */
}

/*
 * INT_TM03 (0x32)
 */
void INT_TM03 (void)
{
    /* Start user code for INT_TM03. Do not edit comment generated here */
    /* End user code. Do not edit comment generated here */
}
/*
 * INT_AD0 (0x34)
 */
void INT_AD0 (void)
{
    /* Start user code for INT_AD0. Do not edit comment generated here */
    /* End user code. Do not edit comment generated here */
}

/*
 * INT_RTC (0x36)
 */
void INT_RTC (void)
{
    /* Start user code for INT_RTC. Do not edit comment generated here */
    /* End user code. Do not edit comment generated here */
}

/*
 * INT_ITL (0x38)
 */
void INT_ITL (void)
{
    /* Start user code for INT_ITL. Do not edit comment generated here */
    /* End user code. Do not edit comment generated here */
}

/*
 * INT_KR (0x3A)
 */
void INT_KR (void)
{
    /* Start user code for INT_KR. Do not edit comment generated here */
    /* End user code. Do not edit comment generated here */
}

/*
 * INT_TD/INT_TRJ0 (0x3C)
 */
void INT_TRJ0 (void)
{
    /* Start user code for INT_TRJ0. Do not edit comment generated here */
    /* End user code. Do not edit comment generated here */
}
//void INT_TD (void) { }

/*
 * INT_TRD0 (0x3E)
 */
void INT_TRD0 (void)
{
    /* Start user code for INT_TRD0. Do not edit comment generated here */
    /* End user code. Do not edit comment generated here */
}

/*
 * INT_TRD1 (0x40)
 */
void INT_TRD1 (void)
{
    /* Start user code for INT_TRD1. Do not edit comment generated here */
    /* End user code. Do not edit comment generated here */
}
/*
 * INT_RD/INT_TRG (0x42)
 */
void INT_TRG (void)
{
    /* Start user code for INT_TRG. Do not edit comment generated here */
    /* End user code. Do not edit comment generated here */
}
//void INT_RD (void) { }

/*
 * INT_ED/INT_CLD/INT_BPD/INT_TRX (0x44)
 */
void INT_TRX (void)
{
    /* Start user code for INT_TRX. Do not edit comment generated here */
    /* End user code. Do not edit comment generated here */
}
//void INT_ED (void) { }
//void INT_CLD (void) { }
//void INT_BPD (void) { }

/*
 * INT_P20 (0x46)
 */
void INT_P20 (void)
{
    /* Start user code for INT_P20. Do not edit comment generated here */
    /* End user code. Do not edit comment generated here */
}

/*
 * INT_P21 (0x48)
 */
void INT_P21 (void)
{
    /* Start user code for INT_P21. Do not edit comment generated here */
    /* End user code. Do not edit comment generated here */
}

/*
 * INT_P6/INT_TMKBSTR10 (0x4A)
 */
void INT_P6 (void)
{
    /* Start user code for INT_P6. Do not edit comment generated here */
    /* End user code. Do not edit comment generated here */
}
//void INT_TMKBSTR10 (void) { }

/*
 * INT_P7/INT_TMKBSTP10 (0x4C)
 */
void INT_P7 (void)
{
    /* Start user code for INT_P7. Do not edit comment generated here */
    /* End user code. Do not edit comment generated here */
}
//void INT_TMKBSTP10 (void) { }

/*
 * INT_P8/INT_TMKBSTR11 (0x4E)
 */
void INT_P8 (void)
{
    /* Start user code for INT_P8. Do not edit comment generated here */
    /* End user code. Do not edit comment generated here */
}
//void INT_TMKBSTR11 (void) { }

/*
 * INT_P9/INT_TMKBSTP11 (0x50)
 */
void INT_P9 (void)
{
    /* Start user code for INT_P9. Do not edit comment generated here */
    /* End user code. Do not edit comment generated here */
}
//void INT_TMKBSTP11 (void) { }

/*
 * INT_FL (0x52)
 */
void INT_FL (void)
{
    /* Start user code for INT_FL. Do not edit comment generated here */
    /* End user code. Do not edit comment generated here */
}

/*
 * INT_CMP0/INT_P10 (0x54)
 */
void INT_P10 (void)
{
    /* Start user code for INT_P10. Do not edit comment generated here */
    /* End user code. Do not edit comment generated here */
}
//void INT_CMP0 (void) { }

/*
 * INT_CMP1/INT_P11 (0x56)
 */
void INT_P11 (void)
{
    /* Start user code for INT_P11. Do not edit comment generated here */
    /* End user code. Do not edit comment generated here */
}
//void INT_CMP1 (void) { }

/*
 * INT_FAATRAP (0x58)
 */
void INT_FAATRAP (void)
{
    /* Start user code for INT_FAATRAP. Do not edit comment generated here */
    /* End user code. Do not edit comment generated here */
}

/*
 * INT_CMP2 (0x5A)
 */
void INT_CMP2 (void)
{
    /* Start user code for INT_CMP2. Do not edit comment generated here */
    /* End user code. Do not edit comment generated here */
}

/*
 * INT_CMP3 (0x5C)
 */
void INT_CMP3 (void)
{
    /* Start user code for INT_CMP3. Do not edit comment generated here */
    /* End user code. Do not edit comment generated here */
}

/*
 * INT_TMKB0 (0x5E)
 */
void INT_TMKB0 (void)
{
    /* Start user code for INT_TMKB0. Do not edit comment generated here */
    /* End user code. Do not edit comment generated here */
}

/*
 * INT_TMKB1 (0x60)
 */
void INT_TMKB1 (void)
{
    /* Start user code for INT_TMKB1. Do not edit comment generated here */
    /* End user code. Do not edit comment generated here */
}

/*
 * INT_TMKB2 (0x62)
 */
void INT_TMKB2 (void)
{
    /* Start user code for INT_TMKB2. Do not edit comment generated here */
    /* End user code. Do not edit comment generated here */
}

/*
 * INT_SDD/INT_GCR (0x64)
 */
void INT_GCR (void)
{
    /* Start user code for INT_GCR. Do not edit comment generated here */
    /* End user code. Do not edit comment generated here */
}
//void INT_SDD (void) { }

/*
 * INT_FED/INT_PMC (0x66)
 */
void INT_PMC (void)
{
    /* Start user code for INT_PMC. Do not edit comment generated here */
    /* End user code. Do not edit comment generated here */
}
//void INT_FED (void) { }

/*
 * INT_TMKBSTR00 (0x68)
 */
void INT_TMKBSTR00 (void)
{
    /* Start user code for INT_TMKBSTR00. Do not edit comment generated here */
    /* End user code. Do not edit comment generated here */
}

/*
 * INT_TMKBSTP00 (0x6A)
 */
void INT_TMKBSTP00 (void)
{
    /* Start user code for INT_TMKBSTP00. Do not edit comment generated here */
    /* End user code. Do not edit comment generated here */
}

/*
 * INT_TMKBSTR01 (0x6C)
 */
void INT_TMKBSTR01 (void)
{
    /* Start user code for INT_TMKBSTR01. Do not edit comment generated here */
    /* End user code. Do not edit comment generated here */
}

/*
 * INT_TMKBSTP01 (0x6E)
 */
void INT_TMKBSTP01 (void)
{
    /* Start user code for INT_TMKBSTP01. Do not edit comment generated here */
    /* End user code. Do not edit comment generated here */
}
/*
 * INT_TMKBSTR20 (0x70)
 */
void INT_TMKBSTR20 (void)
{
    /* Start user code for INT_TMKBSTR20. Do not edit comment generated here */
    /* End user code. Do not edit comment generated here */
}

/*
 * INT_TMKBSTP20 (0x72)
 */
void INT_TMKBSTP20 (void)
{
    /* Start user code for INT_TMKBSTP20. Do not edit comment generated here */
    /* End user code. Do not edit comment generated here */
}

/*
 * INT_TMKBSTR21 (0x74)
 */
void INT_TMKBSTR21 (void)
{
    /* Start user code for INT_TMKBSTR21. Do not edit comment generated here */
    /* End user code. Do not edit comment generated here */
}

/*
 * INT_TMKBSTP21 (0x76)
 */
void INT_TMKBSTP21 (void)
{
    /* Start user code for INT_TMKBSTP21. Do not edit comment generated here */
    /* End user code. Do not edit comment generated here */
}

/*
 * INT_TIMEC1 (0x78)
 */
void INT_TIMEC1 (void)
{
    /* Start user code for INT_TIMEC1. Do not edit comment generated here */
    /* End user code. Do not edit comment generated here */
}

/*
 * INT_TIMEC2 (0x7A)
 */
void INT_TIMEC2 (void)
{
    /* Start user code for INT_TIMEC2. Do not edit comment generated here */
    /* End user code. Do not edit comment generated here */
}
/*
 * INT_AD3 (0x7C)
 */
void INT_AD3 (void)
{
    /* Start user code for INT_AD3. Do not edit comment generated here */
    /* End user code. Do not edit comment generated here */
}

/*
 * INT_BRK_I (0x7E)
 */
void INT_BRK_I (void)
{
    /* Start user code for INT_BRK_I. Do not edit comment generated here */
    /* End user code. Do not edit comment generated here */
}
