Nobutarou/NiMH_Charger_DIY/v6.0/e2studio/NiMHCharger6.0/src/smc_gen/general/r_cg_sau.h

/*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
* Copyright (C) 2021, 2025 Renesas Electronics Corporation. All rights reserved.
***********************************************************************************************************************/

/***********************************************************************************************************************
* File Name        : r_cg_sau.h
* Version          : 1.0.50
* Device(s)        : R7F101G6ExSP
* Description      : General header file for SAU peripheral.
***********************************************************************************************************************/


#ifndef SAU_H
#define SAU_H

/***********************************************************************************************************************
Macro definitions (Register bit)
***********************************************************************************************************************/
/*
    Peripheral Enable Register 0 (PER0)
*/
/* Control of SAU1 input clock (SAU1EN) */
#define _00_SAU1_CLOCK_STOP              (0x00U)    /* stops supply of input clock */
#define _08_SAU1_CLOCK_SUPPLY            (0x08U)    /* supplies input clock */
/* Control of SAU0 input clock (SAU0EN) */
#define _00_SAU0_CLOCK_STOP              (0x00U)    /* stops supply of input clock */
#define _04_SAU0_CLOCK_SUPPLY            (0x04U)    /* supplies input clock */

/*
    Peripheral Reset Control Register 0 (PPR0)
*/
/* Peripheral reset control of SAU1 (SAU1RES) */
#define _00_SAU1_RESET_RELEASE           (0x00U)    /* released from the reset state */
#define _08_SAU1_RESET_SET               (0x08U)    /* reset */
/* Peripheral reset control of SAU0 (SAU0RES) */
#define _00_SAU0_RESET_RELEASE           (0x00U)    /* released from the reset state */
#define _04_SAU0_RESET_SET               (0x04U)    /* reset */

/*
    Serial Clock Select Register m (SPSm)
*/
/* Section of operation clock (CKm1) (PRSm13 - PRSm10) */
#define _0000_SAU_CK01_FCLK_0            (0x0000U)    /* ck01 - fCLK */
#define _0010_SAU_CK01_FCLK_1            (0x0010U)    /* ck01 - fCLK/2^1 */
#define _0020_SAU_CK01_FCLK_2            (0x0020U)    /* ck01 - fCLK/2^2 */
#define _0030_SAU_CK01_FCLK_3            (0x0030U)    /* ck01 - fCLK/2^3 */
#define _0040_SAU_CK01_FCLK_4            (0x0040U)    /* ck01 - fCLK/2^4 */
#define _0050_SAU_CK01_FCLK_5            (0x0050U)    /* ck01 - fCLK/2^5 */
#define _0060_SAU_CK01_FCLK_6            (0x0060U)    /* ck01 - fCLK/2^6 */
#define _0070_SAU_CK01_FCLK_7            (0x0070U)    /* ck01 - fCLK/2^7 */
#define _0080_SAU_CK01_FCLK_8            (0x0080U)    /* ck01 - fCLK/2^8 */
#define _0090_SAU_CK01_FCLK_9            (0x0090U)    /* ck01 - fCLK/2^9 */
#define _00A0_SAU_CK01_FCLK_10           (0x00A0U)    /* ck01 - fCLK/2^10 */
#define _00B0_SAU_CK01_FCLK_11           (0x00B0U)    /* ck01 - fCLK/2^11 */
#define _00C0_SAU_CK01_FCLK_12           (0x00C0U)    /* ck01 - fCLK/2^12 */
#define _00D0_SAU_CK01_FCLK_13           (0x00D0U)    /* ck01 - fCLK/2^13 */
#define _00E0_SAU_CK01_FCLK_14           (0x00E0U)    /* ck01 - fCLK/2^14 */
#define _00F0_SAU_CK01_FCLK_15           (0x00F0U)    /* ck01 - fCLK/2^15 */
#define _000F_SAU_CK01_CLEAR             (0x000FU)    /* clear bit4 - bit7 */
/* Section of operation clock (CKm0) (PRSm03 - PRSm00) */
#define _0000_SAU_CK00_FCLK_0            (0x0000U)    /* ck00 - fCLK */
#define _0001_SAU_CK00_FCLK_1            (0x0001U)    /* ck00 - fCLK/2^1 */
#define _0002_SAU_CK00_FCLK_2            (0x0002U)    /* ck00 - fCLK/2^2 */
#define _0003_SAU_CK00_FCLK_3            (0x0003U)    /* ck00 - fCLK/2^3 */
#define _0004_SAU_CK00_FCLK_4            (0x0004U)    /* ck00 - fCLK/2^4 */
#define _0005_SAU_CK00_FCLK_5            (0x0005U)    /* ck00 - fCLK/2^5 */
#define _0006_SAU_CK00_FCLK_6            (0x0006U)    /* ck00 - fCLK/2^6 */
#define _0007_SAU_CK00_FCLK_7            (0x0007U)    /* ck00 - fCLK/2^7 */
#define _0008_SAU_CK00_FCLK_8            (0x0008U)    /* ck00 - fCLK/2^8 */
#define _0009_SAU_CK00_FCLK_9            (0x0009U)    /* ck00 - fCLK/2^9 */
#define _000A_SAU_CK00_FCLK_10           (0x000AU)    /* ck00 - fCLK/2^10 */
#define _000B_SAU_CK00_FCLK_11           (0x000BU)    /* ck00 - fCLK/2^11 */
#define _000C_SAU_CK00_FCLK_12           (0x000CU)    /* ck00 - fCLK/2^12 */
#define _000D_SAU_CK00_FCLK_13           (0x000DU)    /* ck00 - fCLK/2^13 */
#define _000E_SAU_CK00_FCLK_14           (0x000EU)    /* ck00 - fCLK/2^14 */
#define _000F_SAU_CK00_FCLK_15           (0x000FU)    /* ck00 - fCLK/2^15 */
#define _00F0_SAU_CK00_CLEAR             (0x00F0U)    /* clear bit0 - bit3 */

/*
    Serial Mode Register mn (SMRmn)
*/
#define _0020_SAU_SMRMN_INITIALVALUE     (0x0020U)
/* Selection of macro clock (MCK) of channel n (CKSmn) */
#define _0000_SAU_CLOCK_SELECT_CK00      (0x0000U)    /* operation clock CK0 set by PRS register */
#define _8000_SAU_CLOCK_SELECT_CK01      (0x8000U)    /* operation clock CK1 set by PRS register */
/* Selection of transfer clock (TCLK) of channel n (CCSmn) */
#define _0000_SAU_CLOCK_MODE_CKS         (0x0000U)    /* divided operation clock MCK specified by CKSmn bit */
#define _4000_SAU_CLOCK_MODE_TI0N        (0x4000U)    /* clock input from SCK pin (slave transfer in CSI mode) */
/* Selection of start trigger source (STSmn) */
#define _0000_SAU_TRIGGER_SOFTWARE       (0x0000U)    /* only software trigger is valid */
#define _0100_SAU_TRIGGER_RXD            (0x0100U)    /* valid edge of RXD pin */
/* Controls inversion of level of receive data of channel n in UART mode (SISmn0) */
#define _0000_SAU_EDGE_FALL              (0x0000U)    /* falling edge is detected as the start bit */
#define _0040_SAU_EDGE_RISING            (0x0040U)    /* rising edge is detected as the start bit */
/* Setting of operation mode of channel n (MDmn2, MDmn1) */
#define _0000_SAU_MODE_CSI               (0x0000U)    /* CSI mode */
#define _0002_SAU_MODE_UART              (0x0002U)    /* UART mode */
#define _0004_SAU_MODE_IIC               (0x0004U)    /* simplified IIC mode */
/* Selection of interrupt source of channel n (MDmn0) */
#define _0000_SAU_TRANSFER_END           (0x0000U)    /* transfer end interrupt */
#define _0001_SAU_BUFFER_EMPTY           (0x0001U)    /* buffer empty interrupt */

/*
    Serial Communication Operation Setting Register mn (SCRmn)
*/
#define _0004_SAU_SCRMN_INITIALVALUE     (0x0004U)
/* Setting of operation mode of channel n (TXEmn, RXEmn) */
#define _0000_SAU_NOT_COMMUNICATION      (0x0000U)    /* does not start communication */
#define _4000_SAU_RECEPTION              (0x4000U)    /* reception only */
#define _8000_SAU_TRANSMISSION           (0x8000U)    /* transmission only */
#define _C000_SAU_RECEPTION_TRANSMISSION (0xC000U)    /* reception and transmission */
/* Selection of data and clock phase in CSI mode (DAPmn, CKPmn) */
#define _0000_SAU_TIMING_1               (0x0000U)    /* type 1 */
#define _1000_SAU_TIMING_2               (0x1000U)    /* type 2 */
#define _2000_SAU_TIMING_3               (0x2000U)    /* type 3 */
#define _3000_SAU_TIMING_4               (0x3000U)    /* type 4 */
/* Selection of masking of error interrupt signal (EOCmn) */
#define _0000_SAU_INTSRE_MASK            (0x0000U)    /* masks error interrupt INTSREx */
#define _0400_SAU_INTSRE_ENABLE          (0x0400U)    /* enables generation of error interrupt INTSREx */
/* Setting of parity bit in UART mode (PTCmn1 - PTCmn0) */
#define _0000_SAU_PARITY_NONE            (0x0000U)    /* none parity */
#define _0100_SAU_PARITY_ZERO            (0x0100U)    /* zero parity */
#define _0200_SAU_PARITY_EVEN            (0x0200U)    /* even parity */
#define _0300_SAU_PARITY_ODD             (0x0300U)    /* odd parity */
/* Selection of data transfer sequence in CSI and UART modes (DIRmn) */
#define _0000_SAU_MSB                    (0x0000U)    /* msb */
#define _0080_SAU_LSB                    (0x0080U)    /* lsb */
/* Setting of stop bit in UART mode (SLCmn1, SLCmn0) */
#define _0000_SAU_STOP_NONE              (0x0000U)    /* none stop bit */
#define _0010_SAU_STOP_1                 (0x0010U)    /* 1 stop bit */
#define _0020_SAU_STOP_2                 (0x0020U)    /* 2 stop bits */
/* Setting of data length in CSI and UART modes (DLSmn1 - DLSmn0) */
#define _0001_SAU_LENGTH_9               (0x0001U)    /* 9-bit data length */
#define _0002_SAU_LENGTH_7               (0x0002U)    /* 7-bit data length */
#define _0003_SAU_LENGTH_8               (0x0003U)    /* 8-bit data length */

/*
    Serial Output Level Register m (SOLm)
*/
/* Selects inversion of the level of the transmit data of channel n in UART mode (SOLm2) */
#define _0000_SAU_CHANNEL2_NORMAL        (0x0000U)    /* normal bit level */
#define _0004_SAU_CHANNEL2_INVERTED      (0x0004U)    /* inverted bit level */
/* Selects inversion of the level of the transmit data of channel n in UART mode (SOLm0) */
#define _0000_SAU_CHANNEL0_NORMAL        (0x0000U)    /* normal bit level */
#define _0001_SAU_CHANNEL0_INVERTED      (0x0001U)    /* inverted bit level */

/*
    Noise Filter Enable Register 0 (NFEN0)
*/
/* Use of noise filter */
#define _00_SAU_RXD2_FILTER_OFF          (0x00U)    /* noise filter off */
#define _10_SAU_RXD2_FILTER_ON           (0x10U)    /* noise filter on */
#define _00_SAU_RXD1_FILTER_OFF          (0x00U)    /* noise filter off */
#define _04_SAU_RXD1_FILTER_ON           (0x04U)    /* noise filter on */
#define _00_SAU_RXD0_FILTER_OFF          (0x00U)    /* noise filter off */
#define _01_SAU_RXD0_FILTER_ON           (0x01U)    /* noise filter on */

/*
    Format Of Serial Status Register mn (SSRmn)
*/
/* Communication status indication flag of channel n (TSFmn) */
#define _0040_SAU_UNDER_EXECUTE          (0x0040U)    /* communication is under execution */
/* Buffer register status indication flag of channel n (BFFmn) */
#define _0020_SAU_VALID_STORED           (0x0020U)    /* valid data is stored in the SDRmn register */
/* Framing error detection flag of channel n (FEFmn) */
#define _0004_SAU_FRAM_ERROR             (0x0004U)    /* a framing error occurs during UART reception */
/* Parity error detection flag of channel n (PEFmn) */
#define _0002_SAU_PARITY_ERROR           (0x0002U)    /* a parity error occurs or ACK is not detected */
/* Overrun error detection flag of channel n (OVFmn) */
#define _0001_SAU_OVERRUN_ERROR          (0x0001U)    /* an overrun error occurs */

/*
    Serial Channel Start Register m (SSm)
*/
/* Operation start trigger of channel 3 (SSm3) */
#define _0000_SAU_CH3_START_TRG_OFF      (0x0000U)    /* no trigger operation */
#define _0008_SAU_CH3_START_TRG_ON       (0x0008U)    /* sets SEm3 to 1 and enters the communication wait status */
/* Operation start trigger of channel 2 (SSm2) */
#define _0000_SAU_CH2_START_TRG_OFF      (0x0000U)    /* no trigger operation */
#define _0004_SAU_CH2_START_TRG_ON       (0x0004U)    /* sets SEm2 to 1 and enters the communication wait status */
/* Operation start trigger of channel 1 (SSm1) */
#define _0000_SAU_CH1_START_TRG_OFF      (0x0000U)    /* no trigger operation */
#define _0002_SAU_CH1_START_TRG_ON       (0x0002U)    /* sets SEm1 to 1 and enters the communication wait status */
/* Operation start trigger of channel 0 (SSm0) */
#define _0000_SAU_CH0_START_TRG_OFF      (0x0000U)    /* no trigger operation */
#define _0001_SAU_CH0_START_TRG_ON       (0x0001U)    /* sets SEm0 to 1 and enters the communication wait status */

/*
    Serial Channel Stop Register m (STm)
*/
/* Operation stop trigger of channel 3 (STm3) */
#define _0000_SAU_CH3_STOP_TRG_OFF       (0x0000U)    /* no trigger operation */
#define _0008_SAU_CH3_STOP_TRG_ON        (0x0008U)    /* operation is stopped (stop trigger is generated) */
/* Operation stop trigger of channel 2 (STm2) */
#define _0000_SAU_CH2_STOP_TRG_OFF       (0x0000U)    /* no trigger operation */
#define _0004_SAU_CH2_STOP_TRG_ON        (0x0004U)    /* operation is stopped (stop trigger is generated) */
/* Operation stop trigger of channel 1 (STm1) */
#define _0000_SAU_CH1_STOP_TRG_OFF       (0x0000U)    /* no trigger operation */
#define _0002_SAU_CH1_STOP_TRG_ON        (0x0002U)    /* operation is stopped (stop trigger is generated) */
/* Operation stop trigger of channel 0 (STm0) */
#define _0000_SAU_CH0_STOP_TRG_OFF       (0x0000U)    /* no trigger operation */
#define _0001_SAU_CH0_STOP_TRG_ON        (0x0001U)    /* operation is stopped (stop trigger is generated) */

/*
    Format Of Serial Flag Clear Trigger Register mn (SIRmn)
*/
/* Clear trigger of framing error of channel n (FECTmn) */
#define _0004_SAU_SIRMN_FECTMN           (0x0004U)    /* clears the FEFmn bit of the SSRmn register to 0 */
/* Clear trigger of parity error flag of channel n (PECTmn) */
#define _0002_SAU_SIRMN_PECTMN           (0x0002U)    /* clears the PEFmn bit of the SSRmn register to 0 */
/* Clear trigger of overrun error flag of channel n (OVCTmn) */
#define _0001_SAU_SIRMN_OVCTMN           (0x0001U)    /* clears the OVFmn bit of the SSRmn register to 0 */

/*
    Serial Output Enable Register m (SOEm)
*/
/* Serial output enable/disable of channel 3 (SOEm3) */
#define _0008_SAU_CH3_OUTPUT_ENABLE      (0x0008U)    /* enables output by serial communication operation */
#define _0000_SAU_CH3_OUTPUT_DISABLE     (0x0000U)    /* stops output by serial communication operation */
/* Serial output enable/disable of channel 2 (SOEm2) */
#define _0004_SAU_CH2_OUTPUT_ENABLE      (0x0004U)    /* enables output by serial communication operation */
#define _0000_SAU_CH2_OUTPUT_DISABLE     (0x0000U)    /* stops output by serial communication operation */
/* Serial output enable/disable of channel 1 (SOEm1) */
#define _0002_SAU_CH1_OUTPUT_ENABLE      (0x0002U)    /* enables output by serial communication operation */
#define _0000_SAU_CH1_OUTPUT_DISABLE     (0x0000U)    /* stops output by serial communication operation */
/* Serial output enable/disable of channel 0 (SOEm0) */
#define _0001_SAU_CH0_OUTPUT_ENABLE      (0x0001U)    /* enables output by serial communication operation */
#define _0000_SAU_CH0_OUTPUT_DISABLE     (0x0000U)    /* stops output by serial communication operation */

/*
    Serial Output Register m (SOm)
*/
/* Serial clock output of channel 3 (CKOm3) */
#define _0000_SAU_CH3_CLOCK_OUTPUT_0     (0x0000U)    /* serial clock output value is "0" */
#define _0800_SAU_CH3_CLOCK_OUTPUT_1     (0x0800U)    /* serial clock output value is "1" */
/* Serial clock output of channel 2 (CKOm2) */
#define _0000_SAU_CH2_CLOCK_OUTPUT_0     (0x0000U)    /* serial clock output value is "0" */
#define _0400_SAU_CH2_CLOCK_OUTPUT_1     (0x0400U)    /* serial clock output value is "1" */
/* Serial clock output of channel 1 (CKOm1) */
#define _0000_SAU_CH1_CLOCK_OUTPUT_0     (0x0000U)    /* serial clock output value is "0" */
#define _0200_SAU_CH1_CLOCK_OUTPUT_1     (0x0200U)    /* serial clock output value is "1" */
/* Serial clock output of channel 0 (CKOm0) */
#define _0000_SAU_CH0_CLOCK_OUTPUT_0     (0x0000U)    /* serial clock output value is "0" */
#define _0100_SAU_CH0_CLOCK_OUTPUT_1     (0x0100U)    /* serial clock output value is "1" */
/* Serial data output of channel 3 (SOm3) */
#define _0000_SAU_CH3_DATA_OUTPUT_0      (0x0000U)    /* serial data output value is "0" */
#define _0008_SAU_CH3_DATA_OUTPUT_1      (0x0008U)    /* serial data output value is "1" */
/* Serial data output of channel 2 (SOm2) */
#define _0000_SAU_CH2_DATA_OUTPUT_0      (0x0000U)    /* serial data output value is "0" */
#define _0004_SAU_CH2_DATA_OUTPUT_1      (0x0004U)    /* serial data output value is "1" */
/* Serial data output of channel 1 (SOm1) */
#define _0000_SAU_CH1_DATA_OUTPUT_0      (0x0000U)    /* serial data output value is "0" */
#define _0002_SAU_CH1_DATA_OUTPUT_1      (0x0002U)    /* serial data output value is "1" */
/* Serial data output of channel 0 (SOm0) */
#define _0000_SAU_CH0_DATA_OUTPUT_0      (0x0000U)    /* serial data output value is "0" */
#define _0001_SAU_CH0_DATA_OUTPUT_1      (0x0001U)    /* serial data output value is "1" */

/*
    SAU Standby Control Register m (SSCm)
*/
/* SAU standby wakeup control bit (SWC) */
#define _0000_SAU_CH0_SNOOZE_OFF         (0x0000U)    /* disable start function from STOP state of chip */
#define _0001_SAU_CH0_SNOOZE_ON          (0x0001U)    /* enable start function from STOP state of chip */

/*
    UART Loopback Function Selection Register (ULBS)
*/
/* UART2 loopback function setting (ULBS2) */
#define _00_UART2_LOOPBACK_DISABLE       (0x00U)    /* disable Uart2 loopback function */
#define _04_UART2_LOOPBACK_ENABLE        (0x04U)    /* enable Uart2 loopback function */
/* UART1 loopback function setting (ULBS1) */
#define _00_UART1_LOOPBACK_DISABLE       (0x00U)    /* disable Uart1 loopback function */
#define _02_UART1_LOOPBACK_ENABLE        (0x02U)    /* enable Uart1 loopback function */
/* UART0 loopback function setting (ULBS0) */
#define _00_UART0_LOOPBACK_DISABLE       (0x00U)    /* disable Uart0 loopback function */
#define _01_UART0_LOOPBACK_ENABLE        (0x01U)    /* enable Uart0 loopback function */

/* SAU Used Flag */
#define _00_SAU_IIC_MASTER_FLAG_CLEAR    (0x00U)
#define _01_SAU_IIC_SEND_FLAG            (0x01U)
#define _02_SAU_IIC_RECEIVE_FLAG         (0x02U)
#define _04_SAU_IIC_SENDED_ADDRESS_FLAG  (0x04U)

/*
    Input Switch Control Register (ISC)
*/
/* Channel 0 SSI00 input setting in CSI communication and slave mode (SSIE00) */
#define _00_SAU_SSI00_UNUSED             (0x00U)    /* disables SSI00 pin input */
#define _80_SAU_SSI00_USED               (0x80U)    /* enables SSI00 pin input */

/***********************************************************************************************************************
Macro definitions
***********************************************************************************************************************/

/***********************************************************************************************************************
Typedef definitions
***********************************************************************************************************************/

/***********************************************************************************************************************
Global functions
***********************************************************************************************************************/
/* Start user code for function. Do not edit comment generated here */
/* End user code. Do not edit comment generated here */
#endif
